nickdnj/stoveiq/hardware/pcb/stoveiq.kicad_sch

## KiCad design hardware/pcb/stoveiq.kicad_sch (2026-08-14)

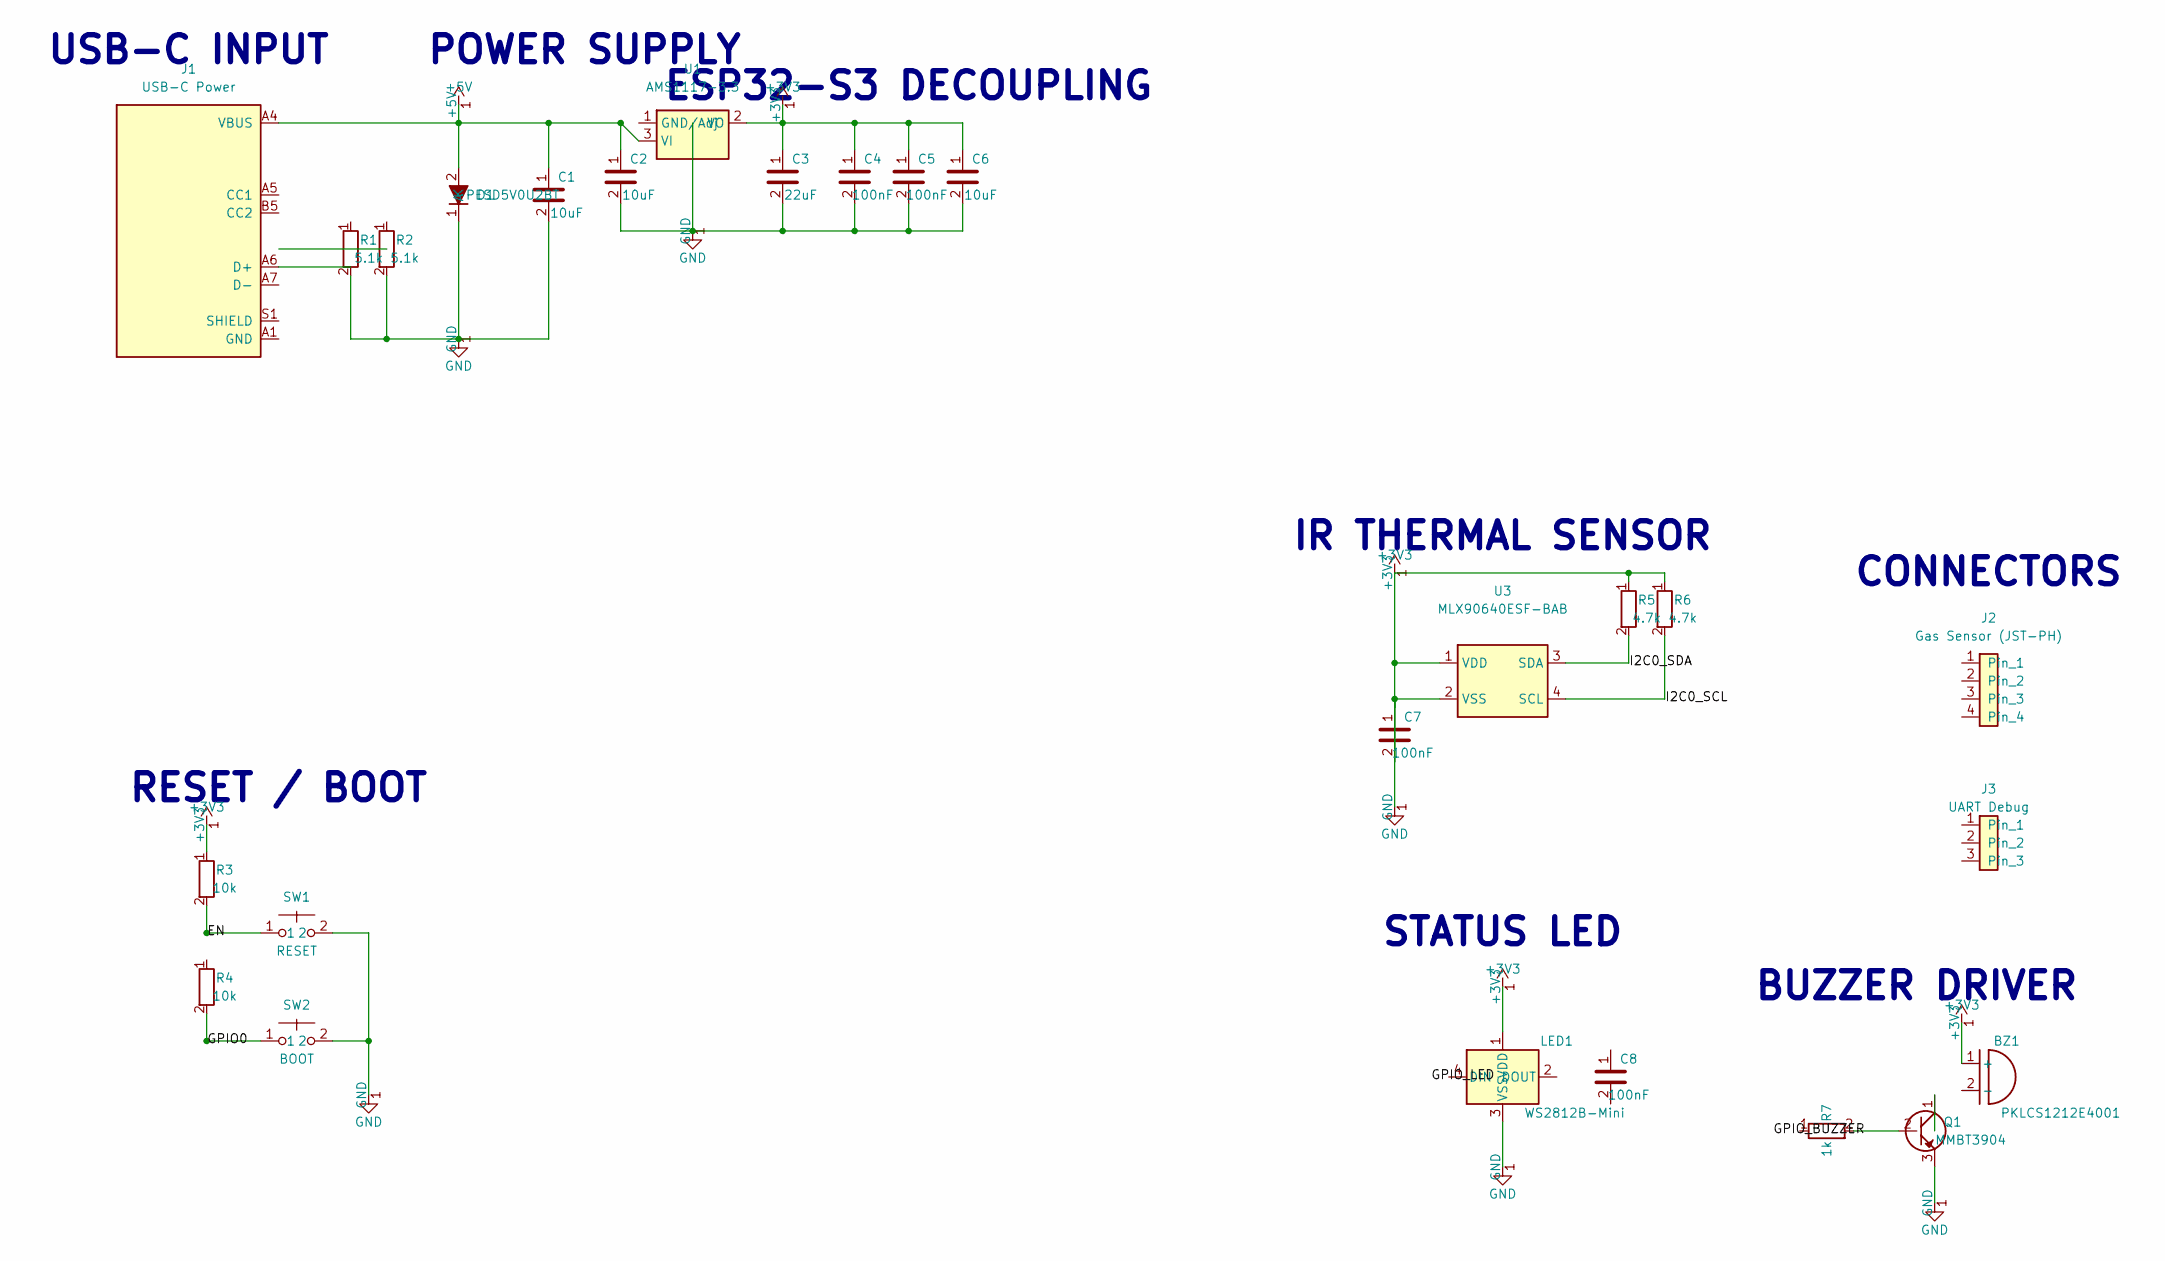
[picture p24: schematic stoveiq.kicad_sch]

Parts:
BZ1: PKLCS1212E4001; Buzzer_12x9.5RM7.6
C1, C2, C6: 10uF; C_0805_2012Metric
C3: 22uF; C_0805_2012Metric
C4, C5, C7, C8: 100nF; C_0402_1005Metric
D1: PESD5V0U2BT; D_SOD-523
J1: USB-C Power; USB_C_Receptacle_GCT_USB4110
J2: Gas Sensor (JST-PH); JST_PH_B4B-PH-K_1x04_P2.00mm_Vertical
J3: UART Debug; PinHeader_1x03_P2.54mm_Vertical
LED1: WS2812B-Mini; LED_WS2812B-Mini_PLCC4_3.5x3.5mm
Q1: MMBT3904; SOT-23
R1, R2: 5.1k; R_0402_1005Metric
R3, R4: 10k; R_0402_1005Metric
R5, R6: 4.7k; R_0402_1005Metric
R7: 1k; R_0402_1005Metric
SW1: RESET; SW_SPST_TL3342
SW2: BOOT; SW_SPST_TL3342
U1: AMS1117-3.3; SOT-223-3_TabPin2
U3: MLX90640ESF-BAB; TO-39-4_Window

Connections:
+3V3: BZ1.1 (+), C1.2, C2.2, C3.1, C3.2, C4.1, C4.2, C5.1, C5.2, C6.1, C6.2, C7.1, C7.2, D1.1 (A), LED1.1 (VDD), LED1.3 (VSS), Q1.3 (E), R1.2, R2.2, R3.1, R5.1, R6.1, SW1.2, SW2.2, U1.2 (VO), U3.1 (VDD), U3.2 (VSS)
+5V: C1.1, C2.1, D1.2 (K), J1.A4 (VBUS), U1.3 (VI)
EN: R3.2, SW1.1
GPIO0: R4.2, SW2.1
I2C0_SCL: R6.2, U3.4 (SCL)
I2C0_SDA: R5.2, U3.3 (SDA)
unnamed: Q1.2 (B), R7.2

Notes on the sheet:
POWER SUPPLY
IR THERMAL SENSOR
STATUS LED
BUZZER DRIVER
CONNECTORS
RESET / BOOT
USB-C INPUT
ESP32-S3 DECOUPLING
